Voxvalve/AQ_Control/LED_Fade_Board/Untitled Sketch_etch_silk_bottom.pdf

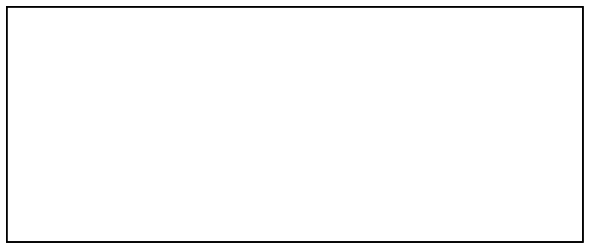
[picture p11: figure]
