Voxvalve/AQ_Control/LED_Fade_Board/Untitled Sketch_etch_silk_bottom_mirror.pdf

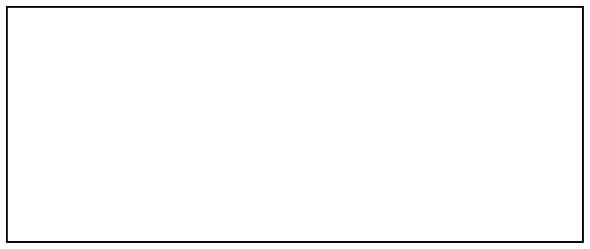
[picture p12: figure]
