Voxvalve/AQ_Control/Status_LED_Board/Status_LED_Board_etch_copper_top.pdf

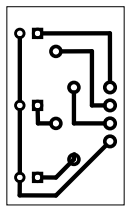
[picture p13: figure]
