Voxvalve/AQ_Control/LED_Fade_Board/Untitled Sketch_etch_silk_top.pdf

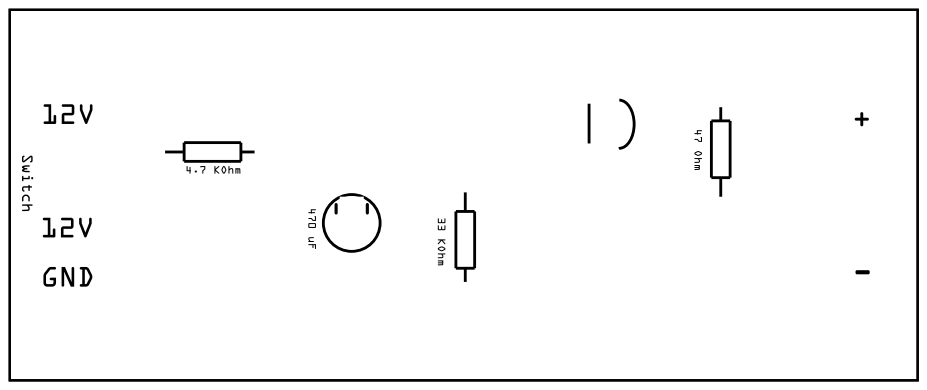
[picture p19: page 1]
