Voxvalve/AQ_Control/LED_Fade_Board/Untitled Sketch_etch_silk_top_mirror.pdf

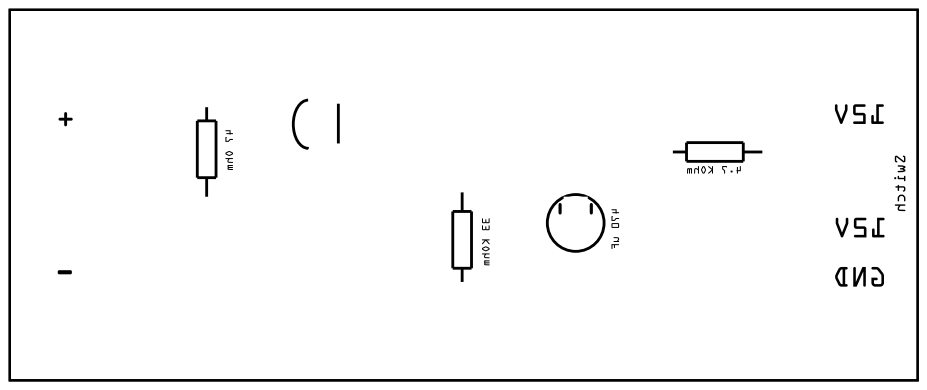
[picture p20: page 1]
