Voxvalve/AQ_Control/LCD_Adapter/LCD_Adapter_PCB2_72900_etch_copper_top.pdf

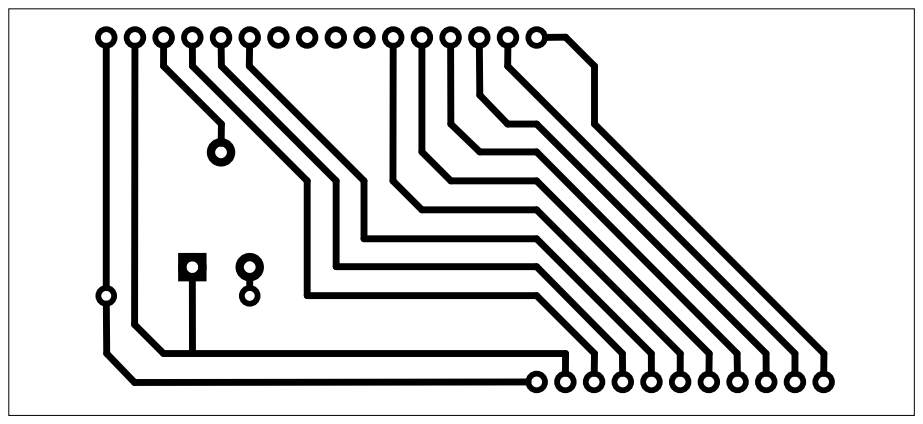
[picture p21: page 1]
