Voxvalve/AQ_Control/LCD_Adapter/LCD_Adapter_PCB2_72900_etch_copper_top_mirror.pdf

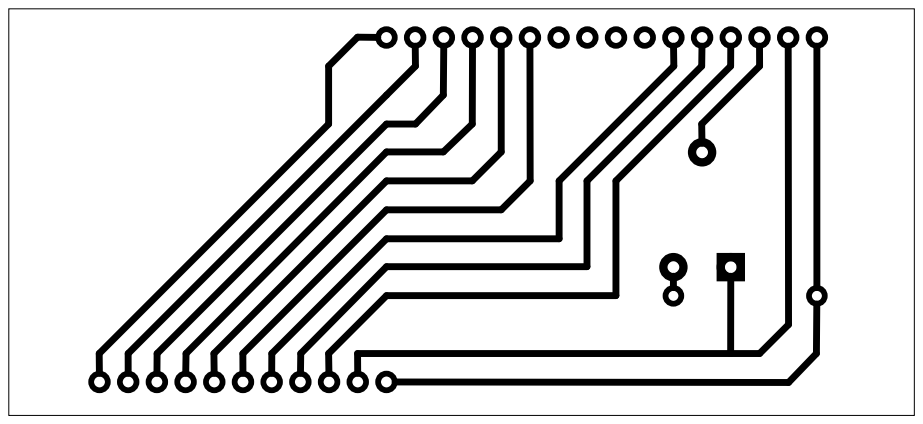
[picture p22: page 1]
