Voxvalve/AQ_Control/AQ_Board/AQ_Board_etch_copper_top.pdf

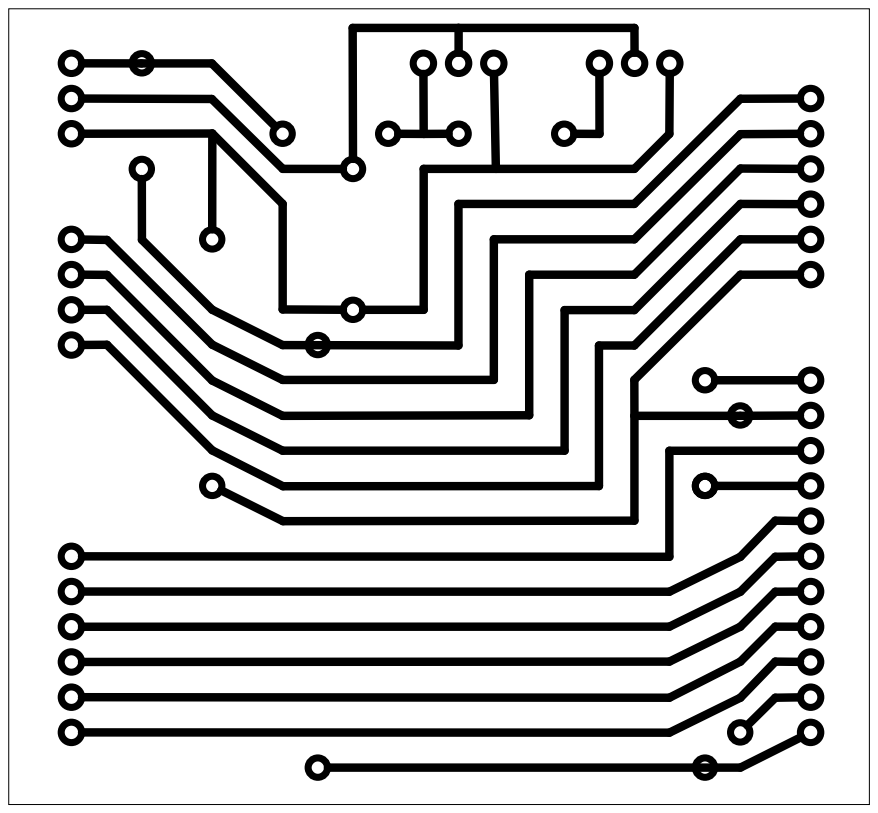
[picture p23: page 1]
