Voxvalve/AQ_Control/AQ_Board/AQ_Board_etch_copper_top_mirror.pdf

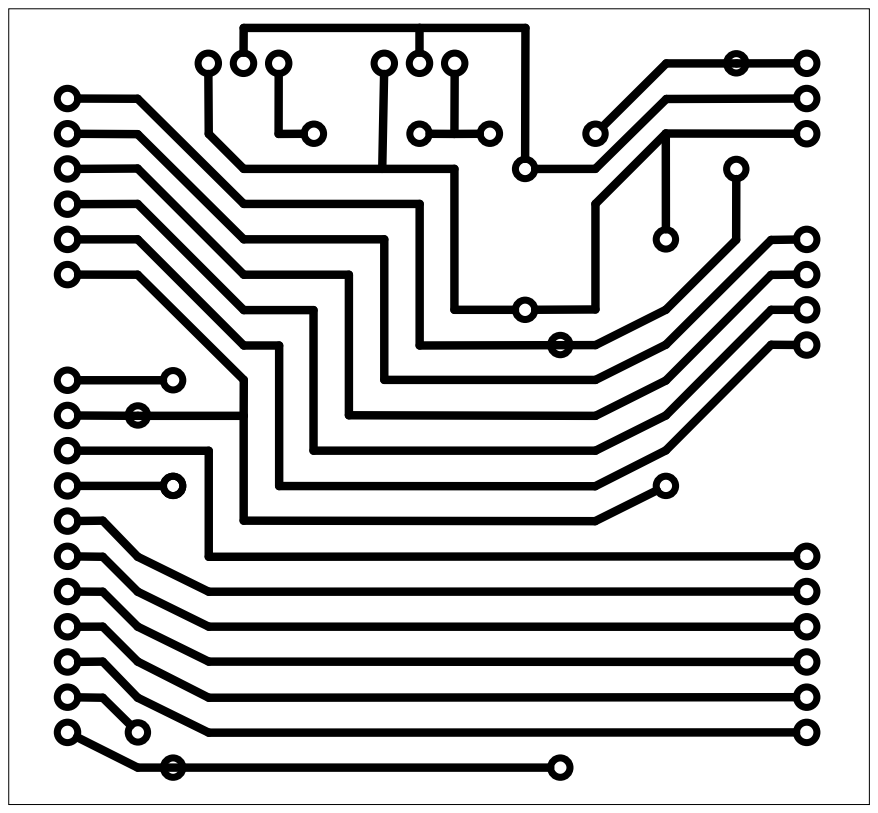
[picture p24: page 1]
